open-headset-interconnect-standard/user-adapter/Documentation/Images/Board Main.JPG

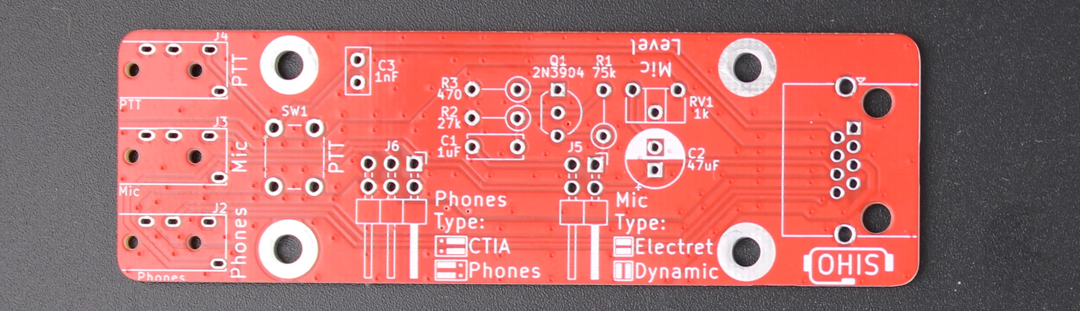
Documentation/Images/Board Main.JPG
