open-headset-interconnect-standard/user-adapter/Documentation/Images/Glamour Oblique 3.5mm side-960px.JPG

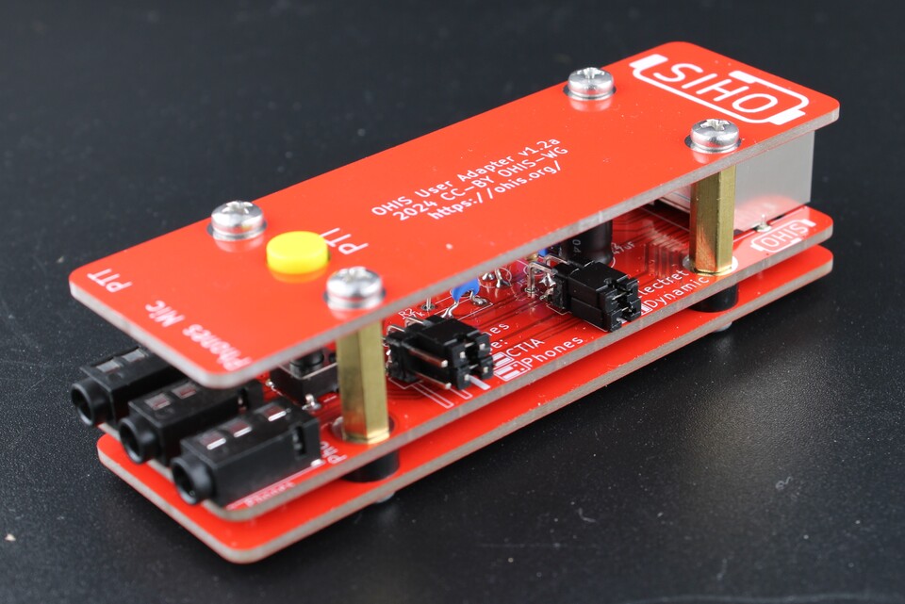
Documentation/Images/Glamour Oblique 3.5mm side-960px.JPG
