open-headset-interconnect-standard/user-adapter/Documentation/Images/Glamour Oblique OHIS side-960px.JPG

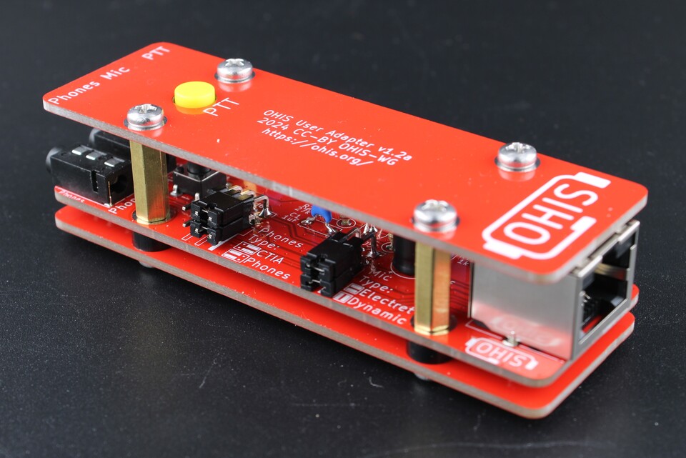
Documentation/Images/Glamour Oblique OHIS side-960px.JPG
