open-headset-interconnect-standard/user-adapter/Documentation/Images/Glamour Side on-960px.JPG

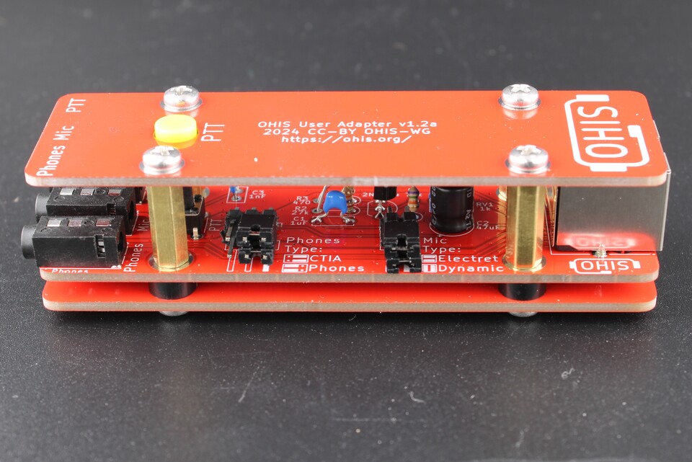
Documentation/Images/Glamour Side on-960px.JPG
