open-headset-interconnect-standard/user-adapter/Documentation/sku:ohis-user-adapter.png

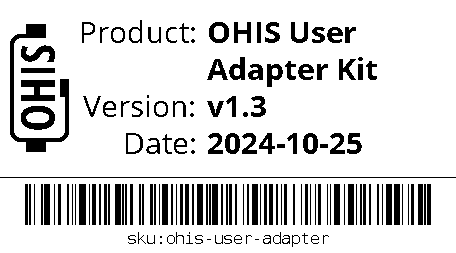
Documentation/sku:ohis-user-adapter.png
